VladimirV01/Universal-Presence-Sensor/Pictures/20250111_104606.jpg

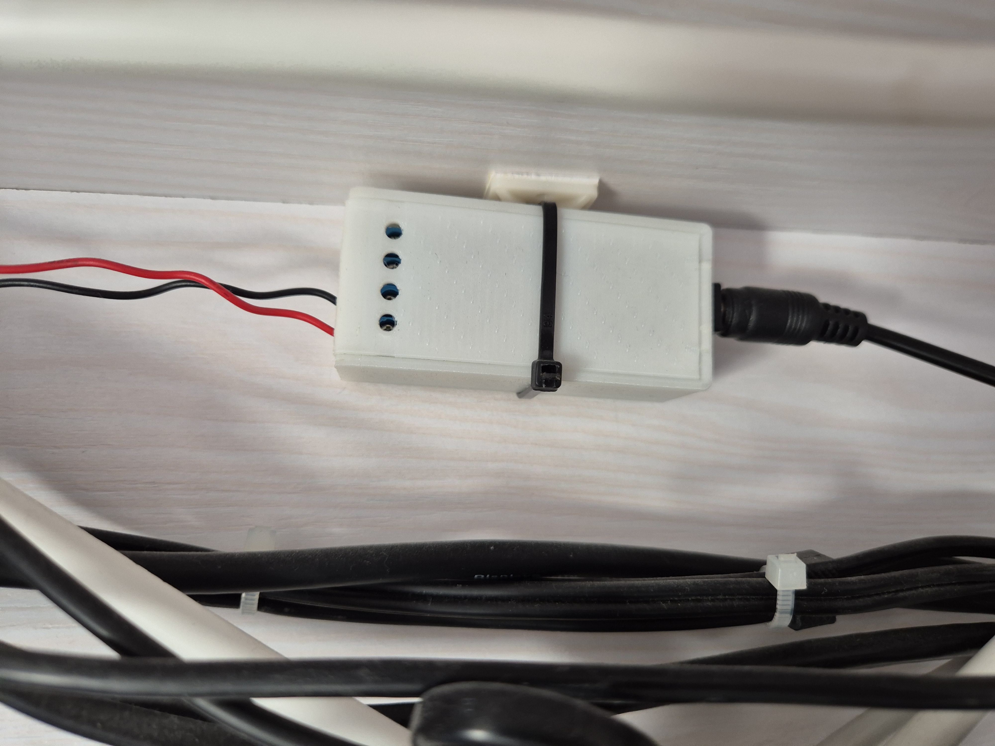
Pictures/20250111_104606.jpg
