VladimirV01/Universal-Presence-Sensor/Pictures/20250111_104653.jpg

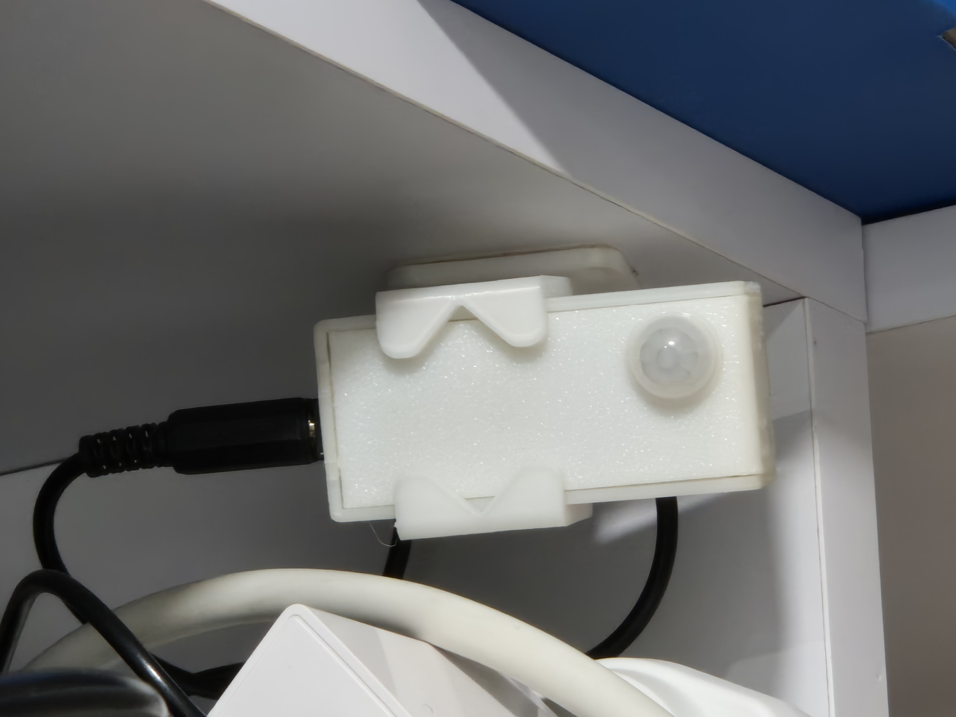
Pictures/20250111_104653.jpg
